PLHFak/Vitrine_lenticulaire/docs/thumbs/base_cplt.jpg

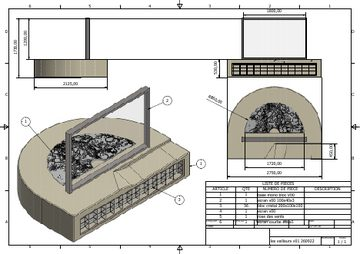
docs/thumbs/base_cplt.jpg
