PLHFak/Vitrine_lenticulaire/docs/ao/LV-AQ-CONS-02_consultation_aquarium_v02-4_NL.pdf

PROJECT
LES VEILLEURS — Beaufort 27

KUNSTENAAR · ONTWERPER
Eva L'Hoest · +32 495 57 92 12 · eva.lhoest@gmail.com

ELEKTROMECHANISCH ASSISTENT
Gioacchino Miceli · +32 497 84 45 10 gioacchino.miceli@thefaktory.com

DOCUMENT
Kristalvitrine — consultatie

ONDERWERP
Rvs kast, glazen deksel, dichting

DOCUMENTNR.
LV-AQ-CONS-02

REVISIE
v02.3

DATUM · UUR
25-09-2026 · 03:10

STATUS
CONSULTATIE

PAGINA
1 / 9

© Eva L'Hoest 2026 — Vertrouwelijk. Reproductie, verspreiding of gebruik buiten deze consultatie verboden zonder schriftelijke toestemming van de kunstenaar. Maten niet contractueel.

# Les Veilleurs — Kristalvitrine (“aquarium”)

Consultatiedossier v02.3 · september 2026 · roestvrijstaalbouw / metaalschrijnwerk — vraag om constructief advies en prijsraming

## 1. Waar gaat het om

Een permanent kunstwerk aan de Belgische kust (Beaufort 27, Noordzee). In de stenen sokkel toont een nis 33 lasergegraveerde optische kristalblokken op een zwarte achtergrond achter een glasplaat, in een droge stikstofatmosfeer die ze beschermt tegen zeevocht. We zoeken een werkplaats om deze nis te bouwen: een gelaste, luchtdichte roestvrijstalen kast en haar afneembaar beglaasd deksel. Het is een uniek, ambachtelijk stuk, gemaakt om minstens tien jaar buiten mee te gaan en ter plaatse geopend en onderhouden te worden. De maten hieronder zijn ons voorstel; uw mening over wat eenvoudiger, veiliger of goedkoper te maken is, interesseert ons evenzeer als uw prijs.

## 2. Hoofdmaten

Element | Maat / waarde | Opmerking
Nuttige binnenholte L × H × D | 2 204 × 333 × ~106 mm | 11 blokken van 200 per rij + 4 mm vulplaatjes; 3 rijen van 100 + 3 mm bovenspeling + 30 mm reserve; diepte: zwarte achtergrond 4 + samengedrukt schuim 8 + blok 100 − de blokken raken het glas, 6 mm vóór het kadervlak
Kast buitenmaat (plaat) | 2 324 × 453 × ~138 mm | = vlak kader van 60 mm rond de holte; 138 = plaat → voorvlak van de lijst = steenvlak
Nis in de stenen sokkel | sponning ≈ 64 × 32 rondom | de kast zit ingebed in de steen; de sponning ontvangt kader + lijst (4 mm speling), het steenvlak ligt gelijk met het glas
Zichtbaar kader vooraan | 60 mm | de kunstenaar wil het zo discreet mogelijk: 50 mm welkom als de sponning het toelaat
Gelaagd extra-helder glas 66.2, antireflex | ≈ 2 264 × 393 × 13 mm — ≈ 29 kg | 2 × 6 mm ijzerarm + PVB; antireflexlaag op de buitenzijde; gepolijste randen
K9-kristalblokken | 33 × (200 × 100 × 100) — ≈ 166 kg | door ons geleverd en geplaatst, ter plaatse
Massa geladen | ≈ 350 kg | kast ≈ 60, kader ≈ 26, klemlijsten ≈ 63, glas ≈ 29, blokken ≈ 166
Klemschroeven | ≈ 110 × M4×30 verzonken Torx, steek 50 | geen enkele schroef gaat door het glas
Dichting | EPDM-koord Ø10, ~30 % samengedrukt in een groef van 2 mm | de aanslag van de lijst bepaalt de samendrukking, niet het aanhaalmoment


PROJECT
LES VEILLEURS — Beaufort 27

DOCUMENT
Kristalvitrine — consultatie

STATUS
CONSULTATIE

PAGINA
2 / 9

PROJECT


LES VEILLEURS — Beaufort 27

DOCUMENT
Kristalvitrine — consultatie

STATUS
CONSULTATIE

PAGINA
3 / 9

## 3. Beschrijving stuk per stuk

3.1 Kast (rvs 316L, plaat 3 mm) — Plaat in U geplooid (achterwand + boven- en onderwand), binnenradius ≤ 3 mm. Twee eindflenzen 3 mm met doorlopende lasnaad, binnennaden vlak geslepen: de holte moet glad blijven, de blokken schuiven tegen de wanden. Verstijvers uitsluitend aan de buitenzijde: 3 horizontale en 4 verticale hoekprofielen 40×40×4, puntgelast (30/150). De achterwand mag niet meer dan 1 mm doorbuigen onder 170 kg verdeelde blokken. Twee buisaansluitingen Ø10 × 1 gelast in de bovenste achterwand, aan beide uiteinden, 200 mm recht, gladde uiteinden (knelkoppeling). Twee afneembare hijsogen M8 bovenaan.
3.2 Voorkader (rvs platstaal 60×10) — Rondom de opening gelast, verstek- of overlappende hoeken, daarna voorvlak na het lassen vlak bewerkt: vlakheid ≤ 0,3 mm/m (dit is het draagvlak van de dichting). Getapte gaten M4, as op 15 mm van de buitenrand, steek 50, twee gaten op 25 mm van elke hoek. Positioneergroef voor het koord: breedte 11, diepte 2, as op 40 mm van de buitenrand (op een derde van de breedte aan de binnenzijde, weg van de glasrand), doorlopend, afgeronde hoeken R10.
3.3 Deksel: vier bewerkte klemlijsten (rvs 316L, 60×24) — Profiel: volle hiel 28×24 die op het kader rust, sponning 32×19 aan de binnenzijde voor het glas (rubberband 1 mm + 13 mm + speling), lip van 5 mm vooraan. Verzonken boringen M4 tegenover de tapgaten. Hoekverbinding voor te stellen door de werkplaats (gedeuvelde en verlijmde verstek, of hoeken uit het volle gefreesd). Zichtbare afwerking: geborsteld of gepolijst, staal af te spreken.

3.4 Glas en plaatsing in de sponning — Gelaagd extra-helder glas 66.2: twee ijzerarme ruiten van 6 mm (type AGC Clearvision, Saint-Gobain Diamant, Pilkington Optiwhite) met twee heldere PVB-folies, dus 13 mm. Antireflexlaag op de buitenzijde (zijde 1) — duurzame magnetroncoating type AGC Clearsight, Pilkington OptiView of Glas Trösch Luxar Classic — zodat de gravures leesbaar blijven onder de Noordzeehemel; geen coating op de binnenzijde, waar de blokken rechtstreeks aanliggen. Gepolijste randen. Geen verlijming: het glas rust in de sponning op een zelfklevende rubberband van ongeveer 1 mm dik en 30 mm breed, gekleefd op de sponningbodem van de lijst; geen glas-metaalcontact, het glas blijft demonteerbaar. Het glas kan van uw gebruikelijke glazenmaker of van de onze komen: geef dit aan in uw antwoord.
3.5 Dichting en schroeven — Vol EPDM-koord Ø10, gevulkaniseerd tot een doorlopend kader op de groefmaten (+ 1 reserve). Schroeven M4×30 verzonken Torx T20 rvs A4, kruiselings aangehaald, ongeveer 2 N·m; de hiel van de lijst komt tegen het kader op 5 mm boven de groefbodem: de samendrukking van de dichting is overal gelijk, ongeacht de ijver van wie schroeft.
3.6 Optie: ledstrip bovenin de kast — Een waterdicht ledprofiel (IP67, 24 V, ~3 W, 3000 K, lengte ≈ 2 100 mm) onder de bovenwand, binnen in de holte, voor neerwaarts strijklicht op de blokken. Wij leveren het profiel; wij vragen u de bevestiging te begroten (twee rails of lippen gelast onder de bovenwand, 3 mm reserve) en een derde dichte aansluiting Ø6 in de bovenste achterwand voor de kabel, met rvs wartel.
3.7 Nis in de steen — De kast zit rondom ingebed in de monolithische stenen sokkel (onder, boven, achter, zijkanten). Vóór het kader is de steen uitgespaard met een sponning van ongeveer 64 mm breed en 32 mm diep die kader en lijst met 4 mm speling opneemt, zodat het steenvlak gelijk ligt met het lijstvlak en het glas. Deze sponning wordt door de steenhouwerij gekapt op basis van uw definitieve maten.

## 4. Tekeningen

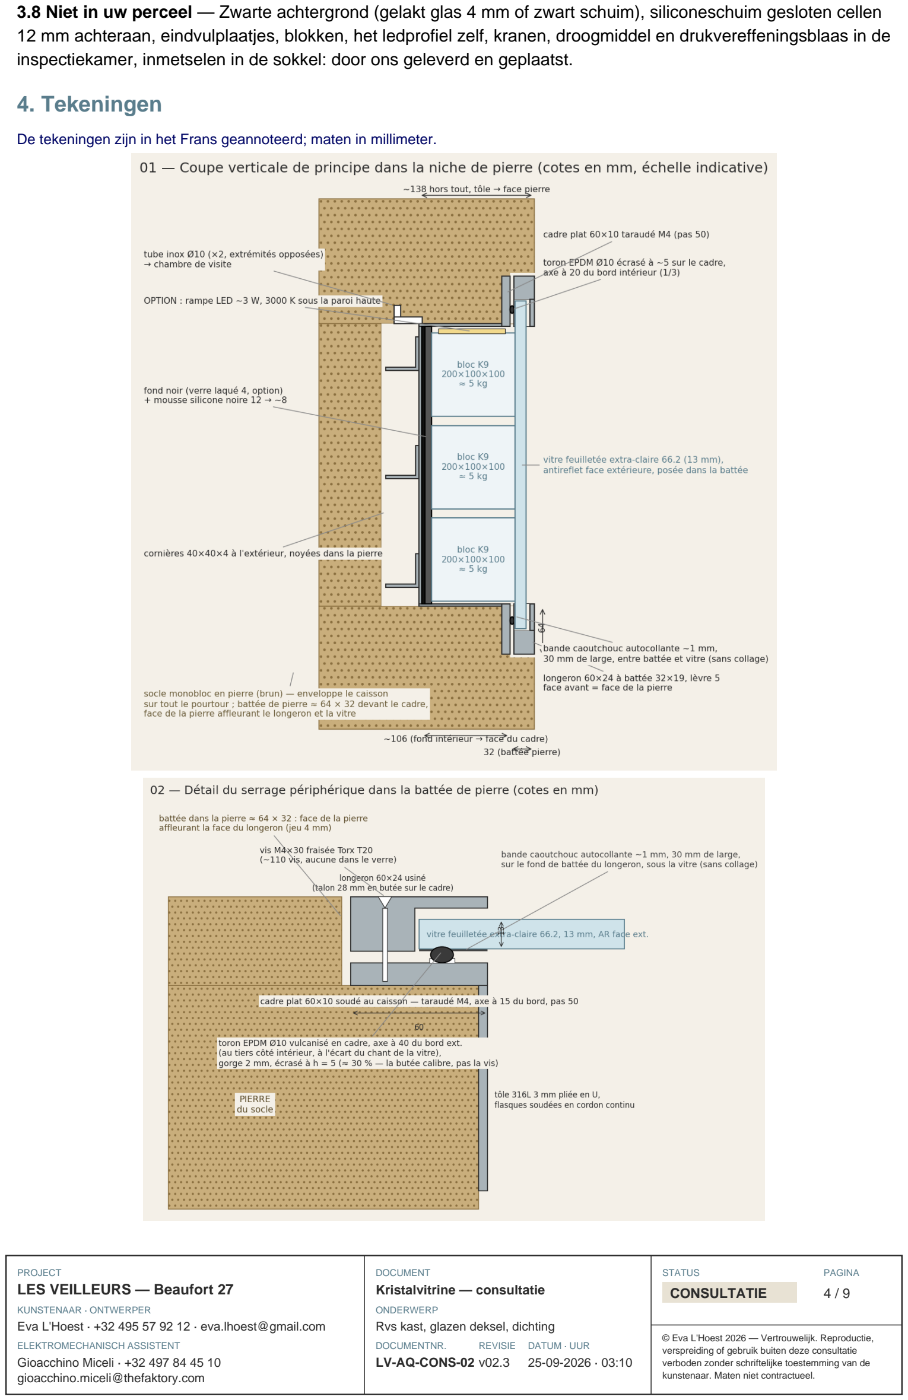
[picture p34: page 4]

PROJECT
LES VEILLEURS — Beaufort 27

DOCUMENT
Kristalvitrine — consultatie

STATUS
CONSULTATIE

PAGINA
4 / 9

3.8 Niet in uw perceel — Zwarte achtergrond (gelakt glas 4 mm of zwart schuim), siliconeschuim gesloten cellen 12 mm achteraan, eindvulplaatjes, blokken, het ledprofiel zelf, kranen, droogmiddel en drukvereffeningsblaas in de inspectiekamer, inmetselen in de sokkel: door ons geleverd en geplaatst.

De tekeningen zijn in het Frans geannoteerd; maten in millimeter.

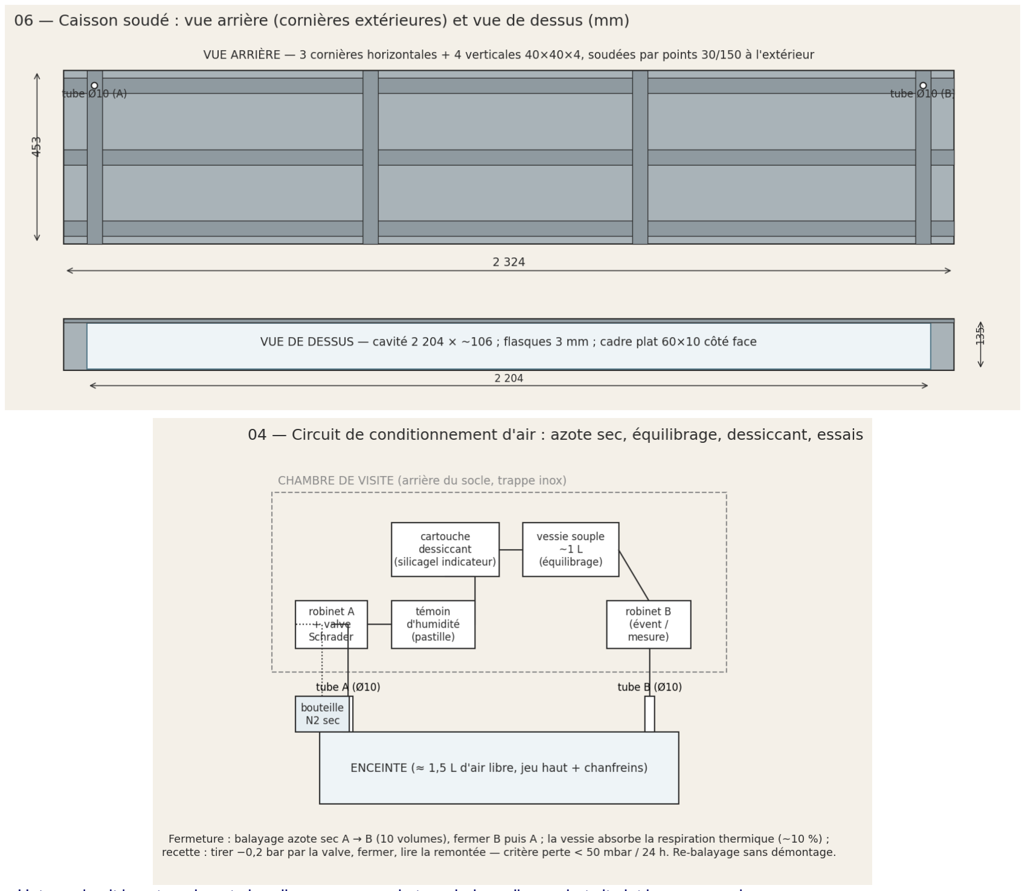
[picture p35: figure]

PROJECT
LES VEILLEURS — Beaufort 27

DOCUMENT
Kristalvitrine — consultatie

STATUS
CONSULTATIE

PAGINA
5 / 9

Het gascircuit is getoond om te begrijpen waarvoor de twee buizen dienen; het zit niet in uw perceel.

## 4 bis. Geëxplodeerde 3D-aanzichten

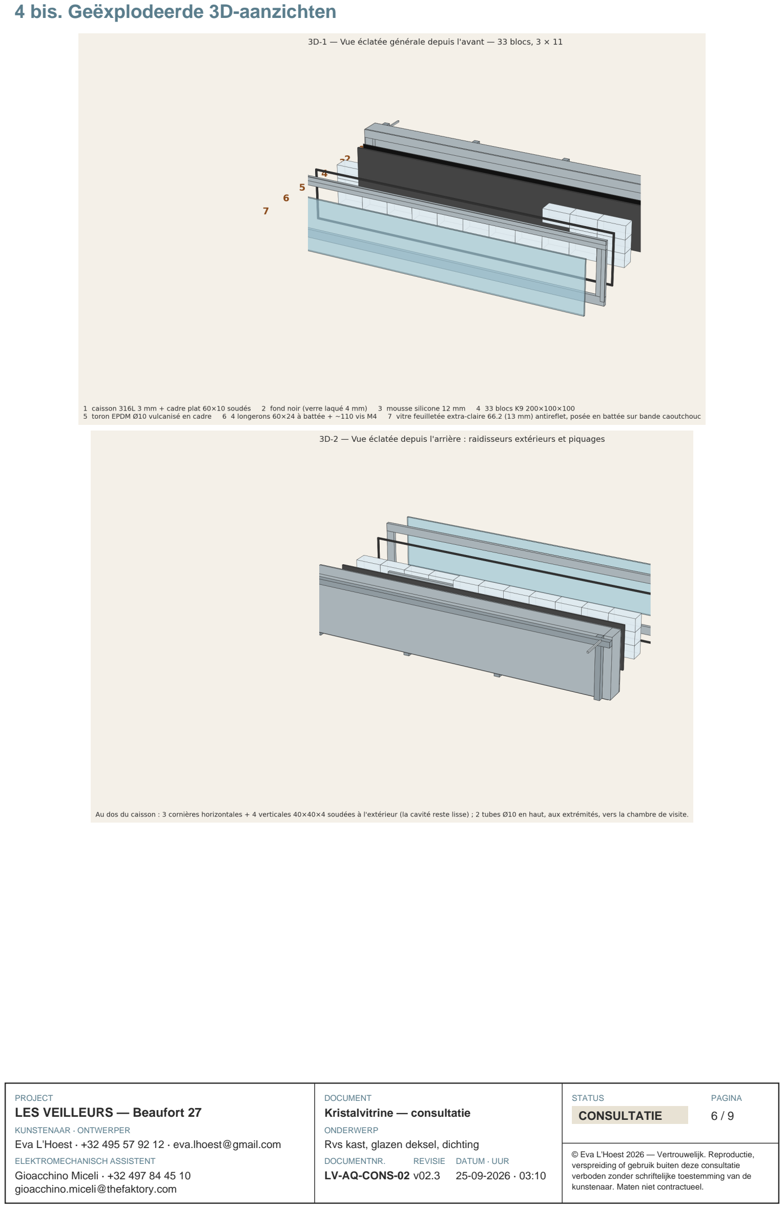
[picture p36: page 6]

PROJECT
LES VEILLEURS — Beaufort 27

DOCUMENT
Kristalvitrine — consultatie

STATUS
CONSULTATIE

PAGINA
6 / 9

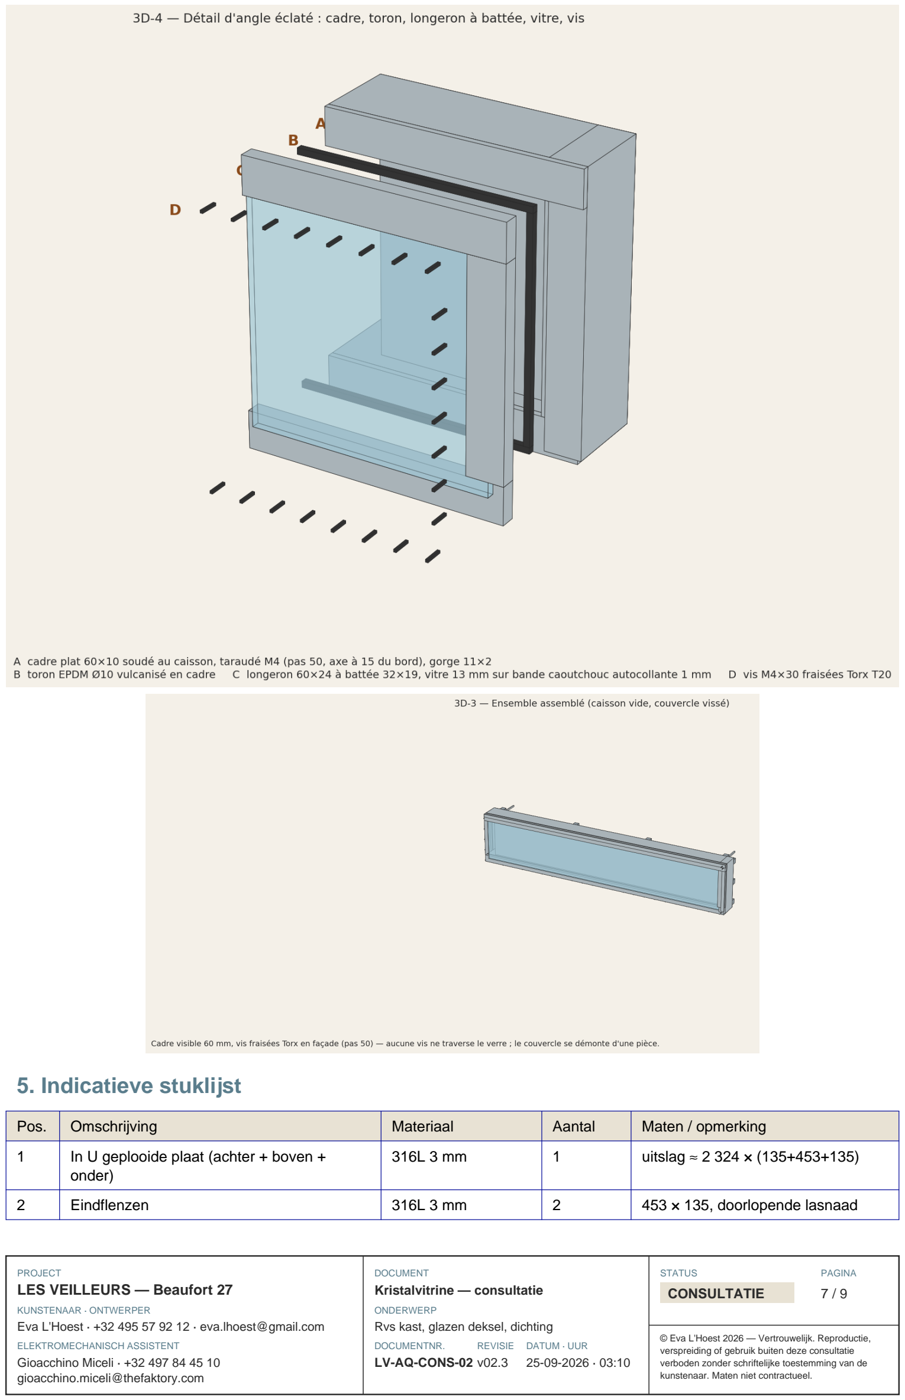
[picture p37: page 7]

PROJECT
LES VEILLEURS — Beaufort 27

DOCUMENT
Kristalvitrine — consultatie

STATUS
CONSULTATIE

PAGINA
7 / 9

## 5. Indicatieve stuklijst

Pos. | Omschrijving | Materiaal | Aantal | Maten / opmerking
1 | In U geplooide plaat (achter + boven + onder) | 316L 3 mm | 1 | uitslag ≈ 2 324 × (135+453+135)
2 | Eindflenzen | 316L 3 mm | 2 | 453 × 135, doorlopende lasnaad

PROJECT
LES VEILLEURS — Beaufort 27

DOCUMENT
Kristalvitrine — consultatie

STATUS
CONSULTATIE

PAGINA
8 / 9
Pos. | Omschrijving | Materiaal | Aantal | Maten / opmerking
3 | Uitwendige verstijvingshoeken | 316L 40×40×4 | 7 | 3 × 2 324 + 4 × 453
4 | Vlak voorkader | 316L 60×10 | ≈ 5,6 m | getapt M4 steek 50, groef 11×2, vlak bewerkt
5 | Klemlijsten met sponning | 316L 60×24 bewerkt | 4 | 2 × 2 324 + 2 × 453 (hoeken te bepalen)
6 | Gelaagd extra-helder antireflexglas | 66.2 ijzerarm, AR zijde 1 | 1 | ≈ 2 264 × 393, gepolijste randen
7 | Zelfklevende rubberband (EPDM of silicone) 30 × 1 mm | rubber | ≈ 6 m | op de sponningbodem van de lijst
8 | EPDM-koord Ø10 gevulkaniseerd kader | EPDM 70 Sh | 1 + 1 | omtrek ≈ 5,5 m
9 | Schroeven M4×30 verzonken Torx T20 | rvs A4 | ≈ 115 | kruiselings aanhalen
10 | Buisaansluitingen Ø10×1 | 316L | 2 | 200 mm, gladde uiteinden
11 | Afneembare hijsogen | rvs M8 | 2 | bovenaan
12 | Led-optie: aansluiting Ø6 + wartel + bevestiging profiel | 316L | 1 | ledprofiel door ons geleverd

## 6. Wat wij u vragen

Perceel | Inhoud | Te begroten
A — Kast | pos. 1 t/m 4, 10, 11: plooien, dicht lassen, verstijvers, vlak kader, tappen, groef | vaste prijs + levertermijn
B — Deksel | pos. 5: 4 bewerkte lijsten, hoekverbinding, boringen, afwerking | vaste prijs + levertermijn
C — Beglazing | pos. 6 en 7: gelaagd extra-helder antireflexglas en rubberband (glas door u of uw glazenmaker) | prijs, of “buiten perceel” als u liever hebt dat wij het leveren
D — Dichting en schroeven | pos. 8 en 9 | prijs
E — Droge test | deksel vastgeschroefd zonder blokken, −0,2 bar via de buizen, 24 u houden (verlies < 50 mbar) | prijs, of inbegrepen
Optie 1 | zichtbaar kader beperkt tot 50 mm (plat 50×10 + lijst 50×24, sponning 24) | meer-/minprijs, haalbaarheid
Optie 2 | zichtbare afwerking van de lijsten: geborsteld / spiegelglans | meerprijs
Optie 3 | ledstrip bovenin de kast: bevestiging onder de bovenwand + dichte aansluiting Ø6 (pos. 12) | meerprijs
Levering | lege kast en gedemonteerd deksel, beschermd, naar een steenhouwerij (België of Zwitserland, nader te bepalen) | transportprijs of af werkplaats

## 7. Uw mening interesseert ons over

- Geplooide plaat 3 mm + uitwendige hoeken: voldoende voor de vlakheid van de achterwand, of verkiest u 4 mm?
- Vlak bewerken van het kader na het lassen: frezen, of volstaat handmatig richten voor ≤ 0,3 mm/m?
- Hoekverbinding van de lijsten: verstek, hoeken uit het volle, of gelast kader in één stuk bewerkt?
- Vol koord (30 %) of hol buiskoord (50 %): wat houdt buiten het langst stand?
- Standaard of onbreekbare (TR) Torx voor de schroeven vooraan?
- Alles wat volgens u de fabricage vereenvoudigt zonder het uitzicht te veranderen: discreet kader, geen schroef in het glas, demonteerbaar.

## 8. Planning en vervolg

PROJECT
LES VEILLEURS — Beaufort 27

DOCUMENT
Kristalvitrine — consultatie

STATUS
CONSULTATIE

PAGINA
9 / 9
Stap | Termijn
Uw constructief advies en prijsraming | binnen 3 weken
Goedkeuring door de kunstenaar, daarna gemaatvoerde uitvoeringstekeningen (PDF + STEP/DXF) | 2 tot 3 weken
Vaste prijs en bestelling | bij ontvangst van de tekeningen
Fabricage en droge test in de werkplaats | 4 tot 6 weken na bestelling
Levering aan de sokkel (hoofdwerkplaats) | samen af te spreken, winter 2026-2027
Een staal van 200 mm klemlijst met koord, rubberband en een stuk glas zou een goede eerste stap zijn: laat ons weten of u dit kunt maken en tegen welke prijs.
