PLHFak/Vitrine_lenticulaire/docs/ao/LV-AQ-PLANS-01_plans_aquarium_EN.pdf

Les Veilleurs — Crystal 'aquarium' showcase — Drawings (LV-AQ-PLANS-01, rev. 1, 29-09-2026)

# Set of drawings for the stainless box lot · drawings labelled in French

1. LV-AQ-PL-01 | Principle vertical section
2. LV-AQ-PL-02 | Detail of the peripheral clamping
3. LV-AQ-PL-03 | Dimensioned front view and plan (3 × 11 blocks)
4. LV-AQ-PL-04 | Gas circuit: dry nitrogen, bladder, desiccant
5. LV-AQ-PL-05 | Assembly sequence
6. LV-AQ-PL-06 | Welded box: rear and top views
7. LV-AQ-PL-07 | Profile of the 60×24 rebated bar
8. LV-AQ-3D-01 | Exploded view from the front
9. LV-AQ-3D-02 | Exploded view from the rear
10. LV-AQ-3D-03 | Assembled unit
11. LV-AQ-3D-04 | Exploded corner detail

Key French terms: caisson = box · cadre = frame · longeron = clamping bar · battée = rebate · vitre = glass pane · toron / joint = gasket cord · vis = screw · piquage = pipe stub · socle = base. Drawings prepared with the help of AI under the team's control — subject to the workshop's shop drawings. Dimensions not contractual.

© Eva L'Hoest 2026 — Confidentiel / Confidential. Cotes non contractuelles / Dimensions not contractual.

# Les Veilleurs — Vitrine « aquarium » des cristaux — Coupe verticale de principe

## LV-AQ-PL-01 · rév. 3 · 25-09-26 · CONSULTATION · schéma légendé en français

PROJET

## LES VEILLEURS — Beaufort 27

ARTISTE · MAÎTRE D'ŒUVRE

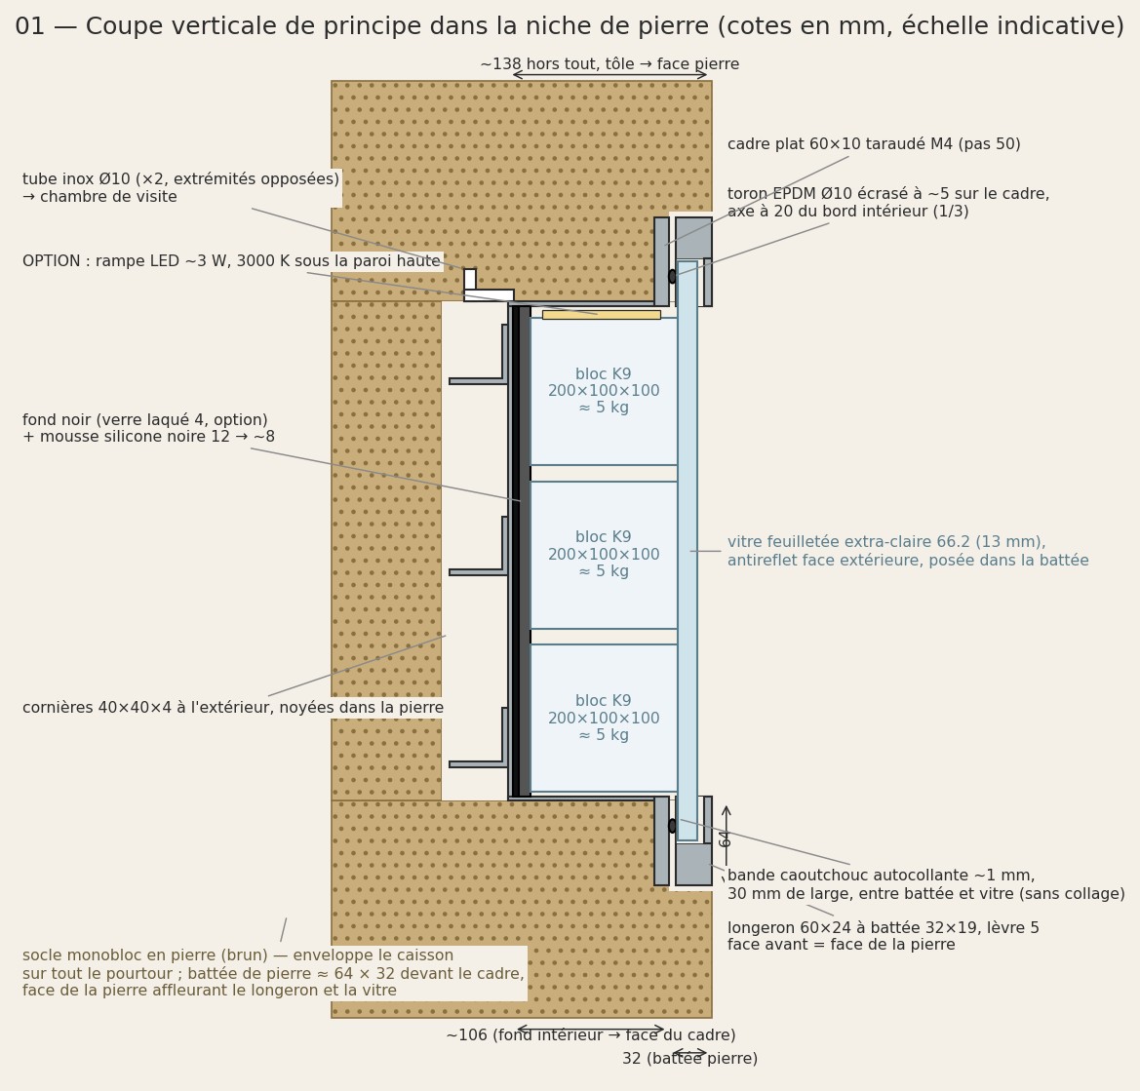
[picture p39: figure]

## Eva L'Hoest · +32 495 57 92 12 · eva.lhoest@gmail.com

ASSISTANT ÉLECTROMÉCANIQUE

## Gioacchino Miceli · +32 497 84 45 10 · gioacchino.miceli@thefaktory.com

DOCUMENT

## Vitrine « aquarium » des cristaux — Coupe verticale de principe

OBJET

## Caisson inox, couvercle vitré, joint et azote sec

N° DOCUMENT · RÉVISION · DATE · HEURE

## LV-AQ-PL-01 · rév. 3 · 25-09-26

EN LIGNE

### https://aquarium-k9.vercel.app

STATUT

## CONSULTATION

© Eva L'Hoest 2026 — Confidentiel. Reproduction, diffusion ou usage hors de cette consultation interdits sans accord écrit de l'artiste. Cotes non contractuelles.

# Les Veilleurs — Vitrine « aquarium » des cristaux — Détail du serrage périphérique

## LV-AQ-PL-02 · rév. 3 · 25-09-26 · CONSULTATION · schéma légendé en français

PROJET

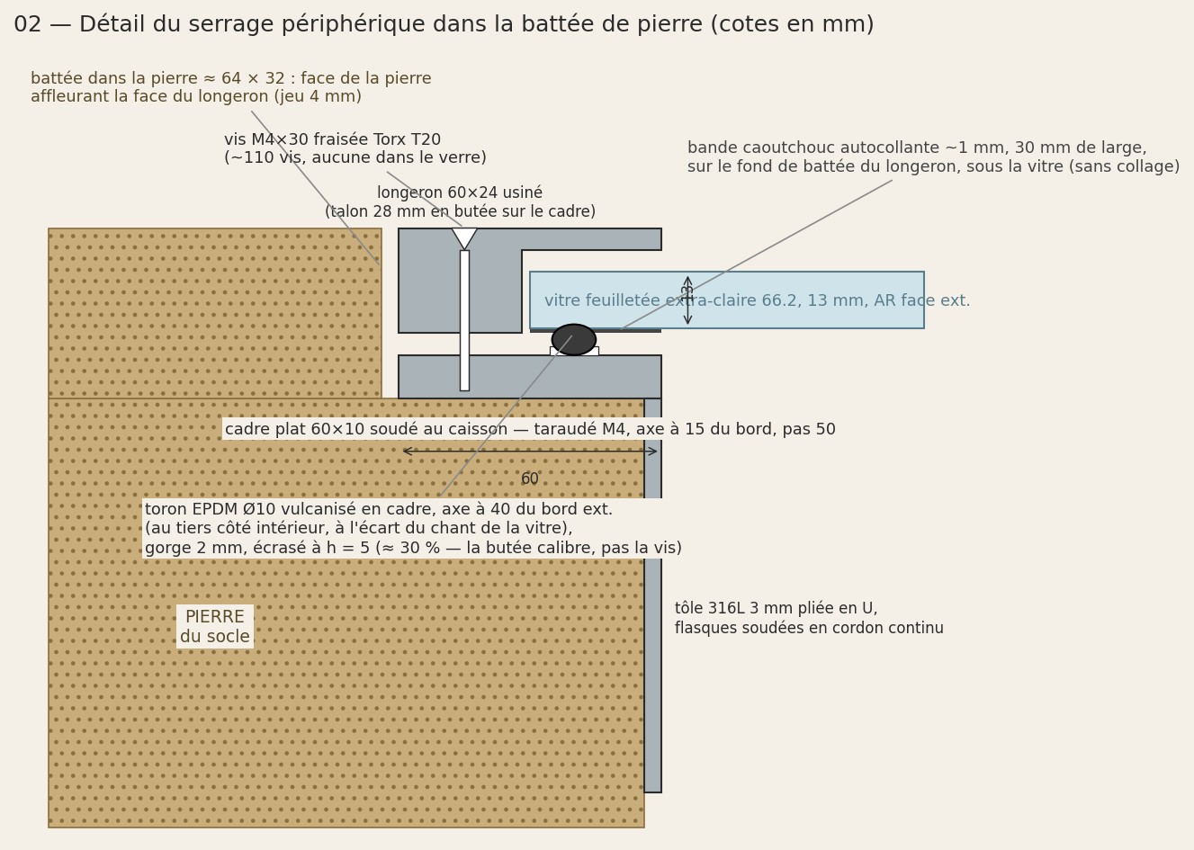
[picture p40: figure]

## LES VEILLEURS — Beaufort 27

ARTISTE · MAÎTRE D'ŒUVRE

## Eva L'Hoest · +32 495 57 92 12 · eva.lhoest@gmail.com

ASSISTANT ÉLECTROMÉCANIQUE

## Gioacchino Miceli · +32 497 84 45 10 · gioacchino.miceli@thefaktory.com

DOCUMENT

## Vitrine « aquarium » des cristaux — Détail du serrage périphérique

OBJET

## Caisson inox, couvercle vitré, joint et azote sec

N° DOCUMENT · RÉVISION · DATE · HEURE

## LV-AQ-PL-02 · rév. 3 · 25-09-26

STATUT

## CONSULTATION

© Eva L'Hoest 2026 — Confidentiel. Reproduction, diffusion ou usage hors de cette consultation interdits sans accord écrit de l'artiste. Cotes non contractuelles.

Les Veilleurs — Vitrine « aquarium » des cristaux — Vue de face et plan cotés (3 × 11 blocs)

## LV-AQ-PL-03 · rév. 2 · 25-09-26 · CONSULTATION · schéma légendé en français

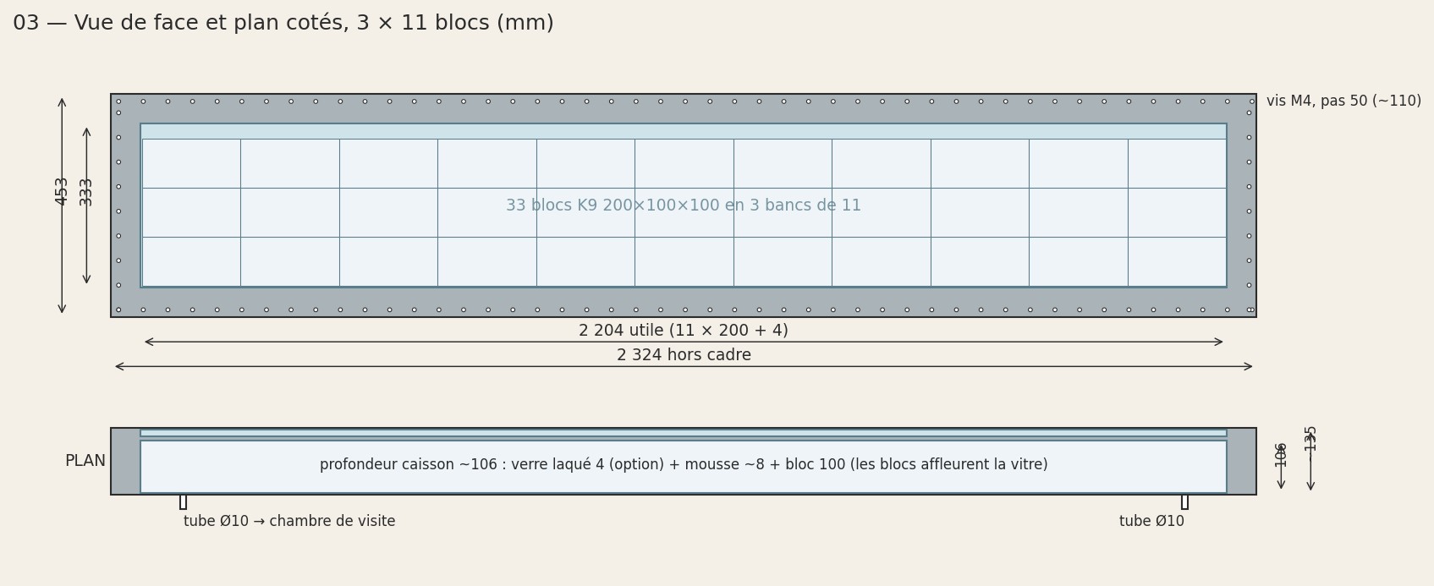
[picture p41: figure]

PROJET

## LES VEILLEURS — Beaufort 27

ARTISTE · MAÎTRE D'ŒUVRE

## Eva L'Hoest · +32 495 57 92 12 · eva.lhoest@gmail.com

ASSISTANT ÉLECTROMÉCANIQUE

## Gioacchino Miceli · +32 497 84 45 10 · gioacchino.miceli@thefaktory.com

DOCUMENT

## Vitrine « aquarium » des cristaux — Vue de face et plan cotés (3 × 11 blocs)

OBJET

## Caisson inox, couvercle vitré, joint et azote sec

N° DOCUMENT · RÉVISION · DATE · HEURE

## LV-AQ-PL-03 · rév. 2 · 25-09-26

STATUT

## CONSULTATION

© Eva L'Hoest 2026 — Confidentiel. Reproduction, diffusion ou usage hors de cette consultation interdits sans accord écrit de l'artiste. Cotes non contractuelles.

Les Veilleurs — Vitrine « aquarium » des cristaux — Circuit gaz : azote sec, vessie, dessiccant

## LV-AQ-PL-04 · rév. 1 · 25-09-26 · CONSULTATION · schéma légendé en français

PROJET

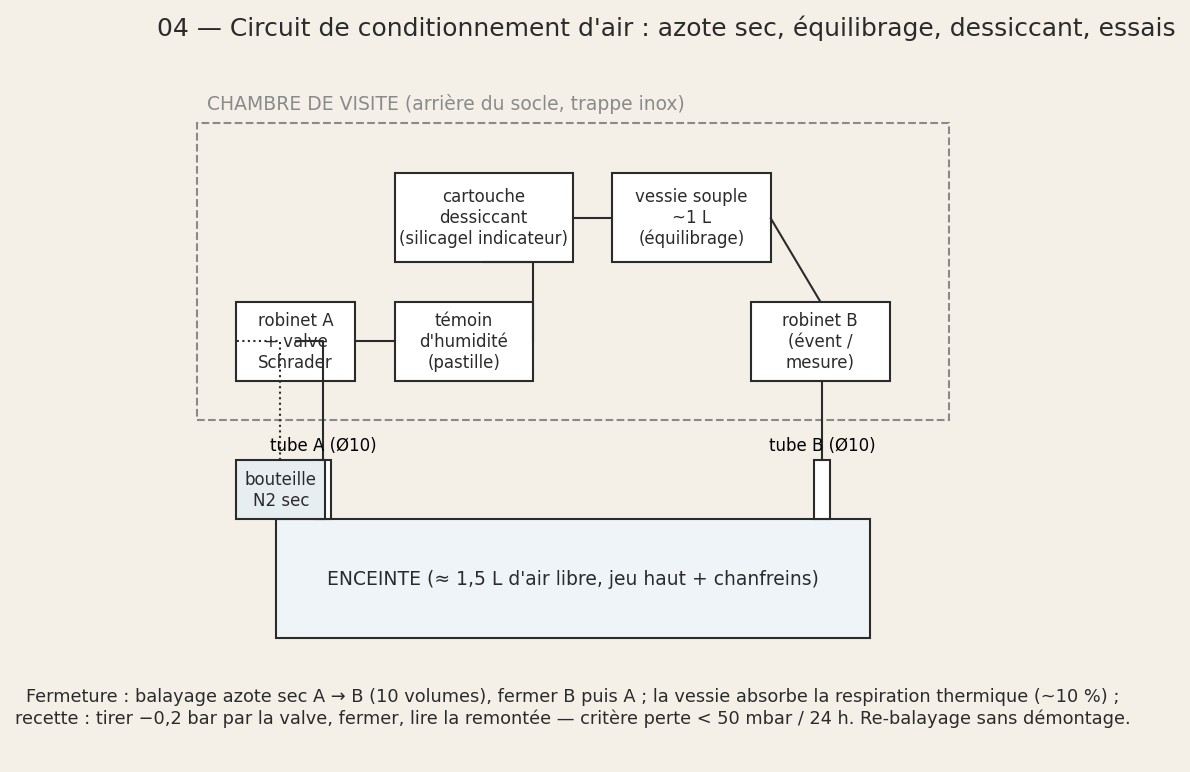
[picture p42: figure]

## LES VEILLEURS — Beaufort 27

ARTISTE · MAÎTRE D'ŒUVRE

## Eva L'Hoest · +32 495 57 92 12 · eva.lhoest@gmail.com

ASSISTANT ÉLECTROMÉCANIQUE

## Gioacchino Miceli · +32 497 84 45 10 · gioacchino.miceli@thefaktory.com

DOCUMENT

## Vitrine « aquarium » des cristaux — Circuit gaz : azote sec, vessie, dessiccant

OBJET

## Caisson inox, couvercle vitré, joint et azote sec

N° DOCUMENT · RÉVISION · DATE · HEURE

## LV-AQ-PL-04 · rév. 1 · 25-09-26

STATUT

## CONSULTATION

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

# Les Veilleurs — Vitrine « aquarium » des cristaux — Séquence de montage

## LV-AQ-PL-05 · rév. 1 · 25-09-26 · CONSULTATION · schéma légendé en français

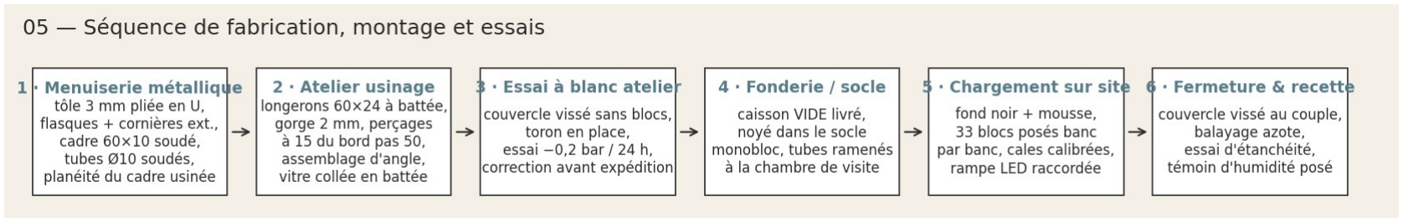
[picture p43: figure]

PROJET

## LES VEILLEURS — Beaufort 27

ARTISTE · MAÎTRE D'ŒUVRE

## Eva L'Hoest · +32 495 57 92 12 · eva.lhoest@gmail.com

ASSISTANT ÉLECTROMÉCANIQUE

## Gioacchino Miceli · +32 497 84 45 10 · gioacchino.miceli@thefaktory.com

DOCUMENT

## Vitrine « aquarium » des cristaux — Séquence de montage

OBJET

## Caisson inox, couvercle vitré, joint et azote sec

N° DOCUMENT · RÉVISION · DATE · HEURE

## LV-AQ-PL-05 · rév. 1 · 25-09-26

STATUT

## CONSULTATION

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

Les Veilleurs — Vitrine « aquarium » des cristaux — Caisson soudé : vue arrière et vue de dessus

## LV-AQ-PL-06 · rév. 1 · 25-09-26 · CONSULTATION · schéma légendé en français

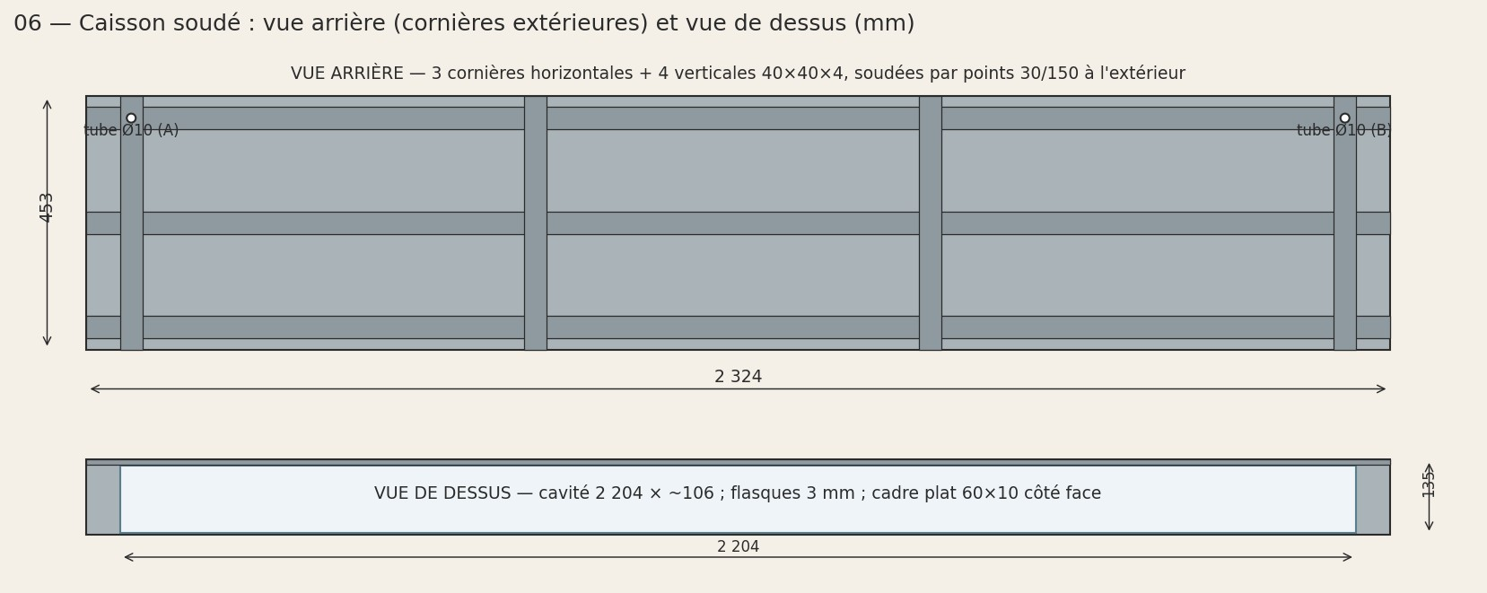
[picture p44: figure]

PROJET

## LES VEILLEURS — Beaufort 27

ARTISTE · MAÎTRE D'ŒUVRE

## Eva L'Hoest · +32 495 57 92 12 · eva.lhoest@gmail.com

ASSISTANT ÉLECTROMÉCANIQUE

## Gioacchino Miceli · +32 497 84 45 10 · gioacchino.miceli@thefaktory.com

DOCUMENT

## Vitrine « aquarium » des cristaux — Caisson soudé : vue arrière et vue de dessus

OBJET

## Caisson inox, couvercle vitré, joint et azote sec

N° DOCUMENT · RÉVISION · DATE · HEURE

## LV-AQ-PL-06 · rév. 1 · 25-09-26

STATUT

## CONSULTATION

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

# Les Veilleurs — Vitrine « aquarium » des cristaux — Profil du longeron à battée 60×24

## LV-AQ-PL-07 · rév. 2 · 25-09-26 · CONSULTATION · schéma légendé en français

PROJET

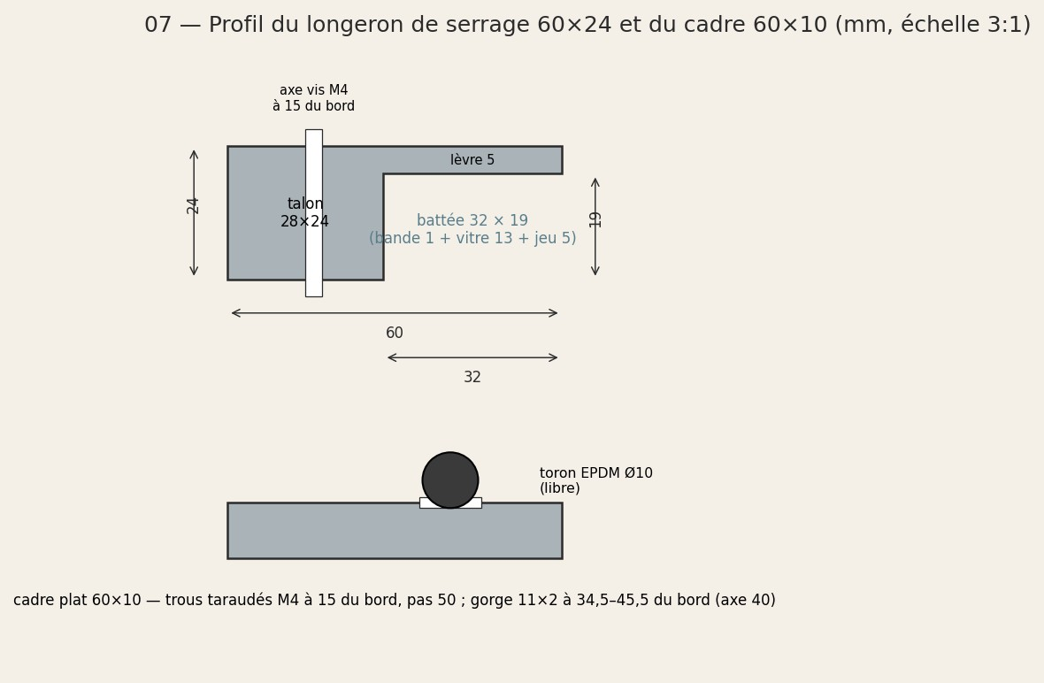
[picture p45: figure]

## LES VEILLEURS — Beaufort 27

ARTISTE · MAÎTRE D'ŒUVRE

## Eva L'Hoest · +32 495 57 92 12 · eva.lhoest@gmail.com

ASSISTANT ÉLECTROMÉCANIQUE

## Gioacchino Miceli · +32 497 84 45 10 · gioacchino.miceli@thefaktory.com

DOCUMENT

## Vitrine « aquarium » des cristaux — Profil du longeron à battée 60×24

OBJET

## Caisson inox, couvercle vitré, joint et azote sec

N° DOCUMENT · RÉVISION · DATE · HEURE

## LV-AQ-PL-07 · rév. 2 · 25-09-26

STATUT

## CONSULTATION

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

# Les Veilleurs — Vitrine « aquarium » des cristaux — Vue éclatée depuis l'avant

## LV-AQ-3D-01 · rév. 1 · 25-09-26 · CONSULTATION · schéma légendé en français

PROJET

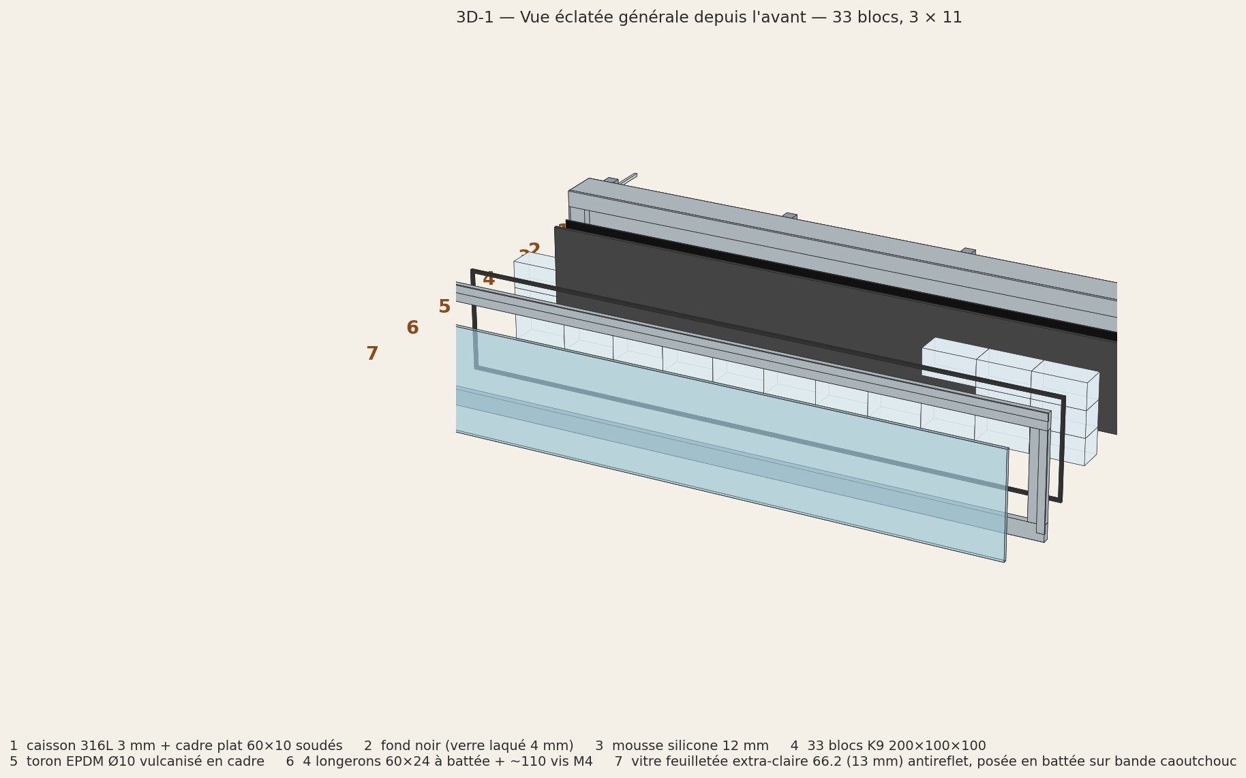
[picture p46: figure]

## LES VEILLEURS — Beaufort 27

ARTISTE · MAÎTRE D'ŒUVRE

## Eva L'Hoest · +32 495 57 92 12 · eva.lhoest@gmail.com

ASSISTANT ÉLECTROMÉCANIQUE

## Gioacchino Miceli · +32 497 84 45 10 · gioacchino.miceli@thefaktory.com

DOCUMENT

## Vitrine « aquarium » des cristaux — Vue éclatée depuis l'avant

OBJET

## Caisson inox, couvercle vitré, joint et azote sec

N° DOCUMENT · RÉVISION · DATE · HEURE

## LV-AQ-3D-01 · rév. 1 · 25-09-26

STATUT

## CONSULTATION

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

# Les Veilleurs — Vitrine « aquarium » des cristaux — Vue éclatée depuis l'arrière

## LV-AQ-3D-02 · rév. 1 · 25-09-26 · CONSULTATION · schéma légendé en français

PROJET

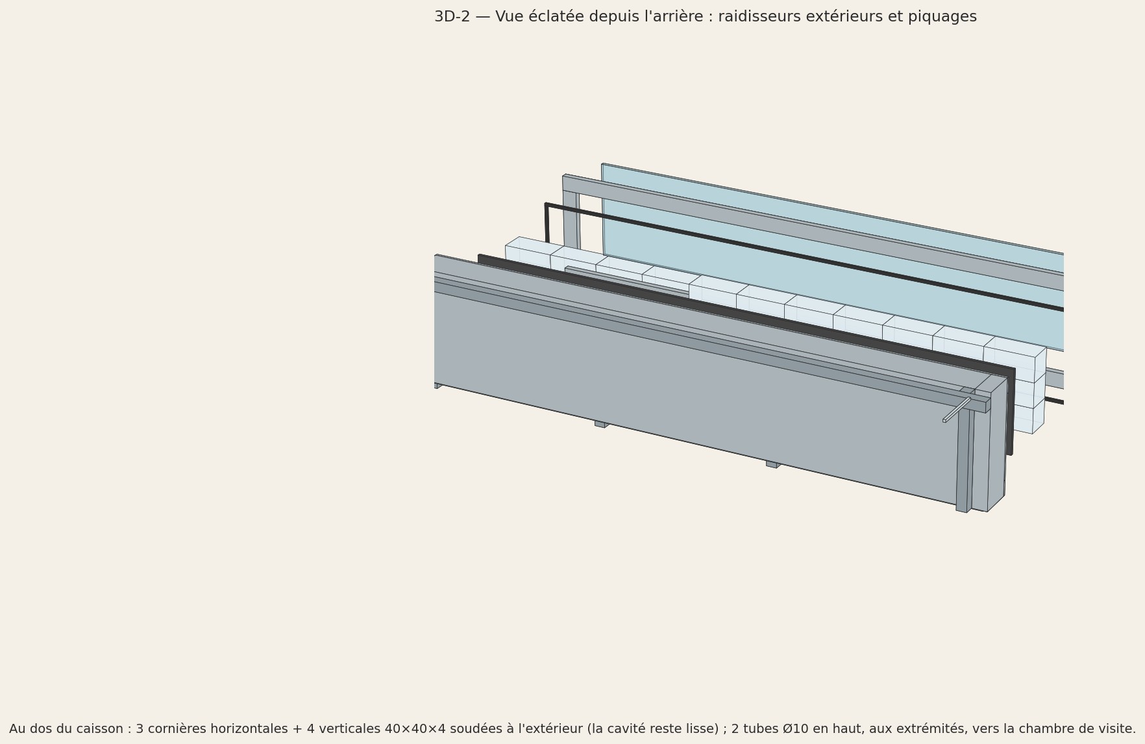
[picture p47: figure]

## LES VEILLEURS — Beaufort 27

ARTISTE · MAÎTRE D'ŒUVRE

## Eva L'Hoest · +32 495 57 92 12 · eva.lhoest@gmail.com

ASSISTANT ÉLECTROMÉCANIQUE

## Gioacchino Miceli · +32 497 84 45 10 · gioacchino.miceli@thefaktory.com

DOCUMENT

## Vitrine « aquarium » des cristaux — Vue éclatée depuis l'arrière

OBJET

## Caisson inox, couvercle vitré, joint et azote sec

N° DOCUMENT · RÉVISION · DATE · HEURE

## LV-AQ-3D-02 · rév. 1 · 25-09-26

STATUT

## CONSULTATION

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

# Les Veilleurs — Vitrine « aquarium » des cristaux — Ensemble assemblé

## LV-AQ-3D-03 · rév. 1 · 25-09-26 · CONSULTATION · schéma légendé en français

PROJET

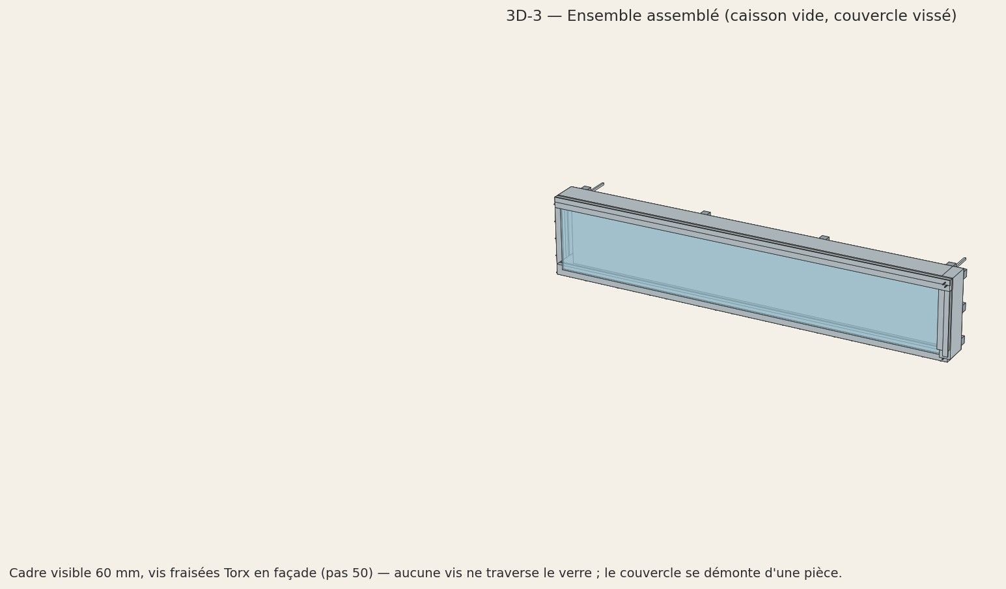
[picture p48: figure]

## LES VEILLEURS — Beaufort 27

ARTISTE · MAÎTRE D'ŒUVRE

## Eva L'Hoest · +32 495 57 92 12 · eva.lhoest@gmail.com

ASSISTANT ÉLECTROMÉCANIQUE

## Gioacchino Miceli · +32 497 84 45 10 · gioacchino.miceli@thefaktory.com

DOCUMENT

## Vitrine « aquarium » des cristaux — Ensemble assemblé

OBJET

## Caisson inox, couvercle vitré, joint et azote sec

N° DOCUMENT · RÉVISION · DATE · HEURE

## LV-AQ-3D-03 · rév. 1 · 25-09-26

STATUT

## CONSULTATION

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

# Les Veilleurs — Vitrine « aquarium » des cristaux — Détail d'angle éclaté

## LV-AQ-3D-04 · rév. 1 · 25-09-26 · CONSULTATION · schéma légendé en français

PROJET

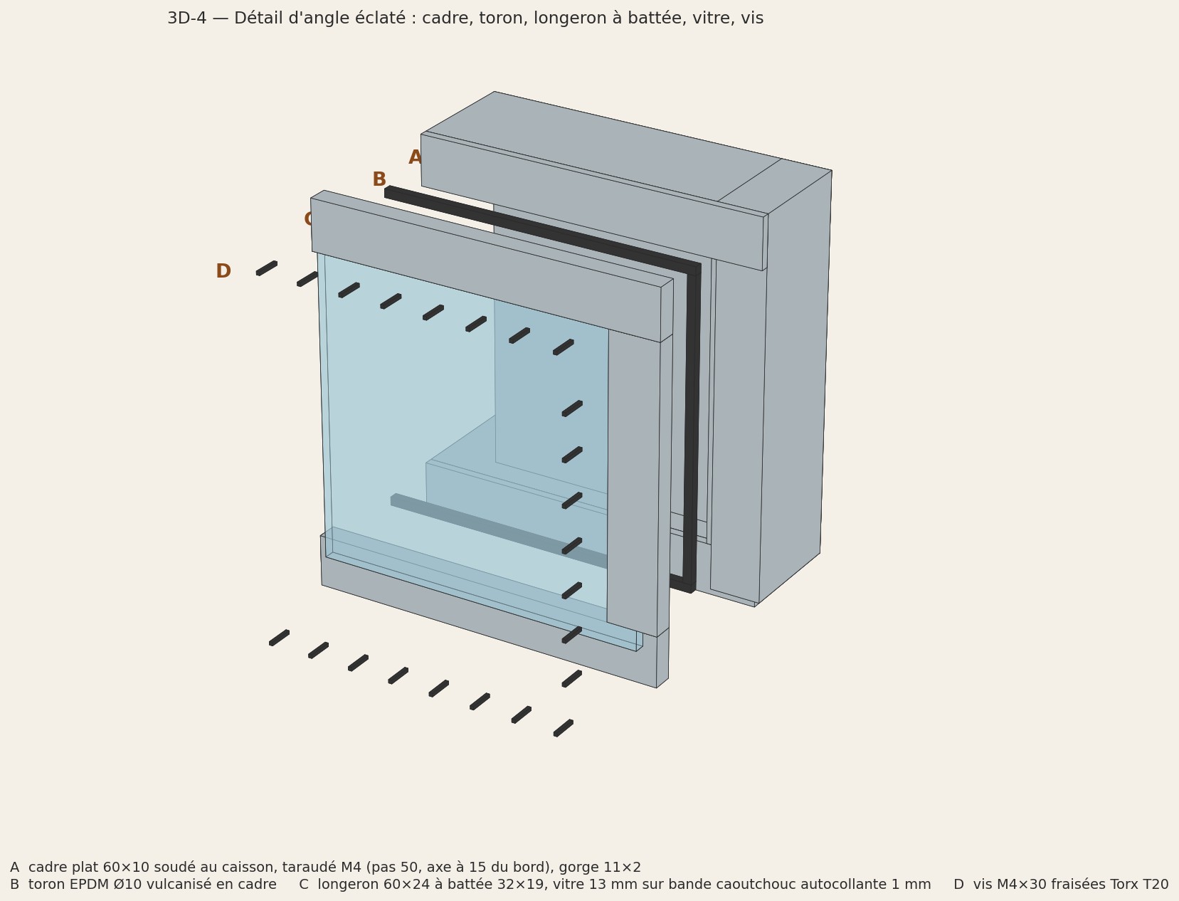
[picture p49: figure]

## LES VEILLEURS — Beaufort 27

ARTISTE · MAÎTRE D'ŒUVRE

## Eva L'Hoest · +32 495 57 92 12 · eva.lhoest@gmail.com

ASSISTANT ÉLECTROMÉCANIQUE

## Gioacchino Miceli · +32 497 84 45 10 · gioacchino.miceli@thefaktory.com

DOCUMENT

## Vitrine « aquarium » des cristaux — Détail d'angle éclaté

OBJET

## Caisson inox, couvercle vitré, joint et azote sec

N° DOCUMENT · RÉVISION · DATE · HEURE

## LV-AQ-3D-04 · rév. 1 · 25-09-26

STATUT

## CONSULTATION

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
