PLHFak/Vitrine_lenticulaire/docs/pdf/LV-VL-CRQ-01_croquis.pdf

Les Veilleurs — La vitrine lenticulaire — Croquis de principe d'origine — coupe dans le montant

## LV-VL-CRQ-01 · rév. 1 · 24-09-26 · ESQUISSE · schéma légendé en français

PROJET

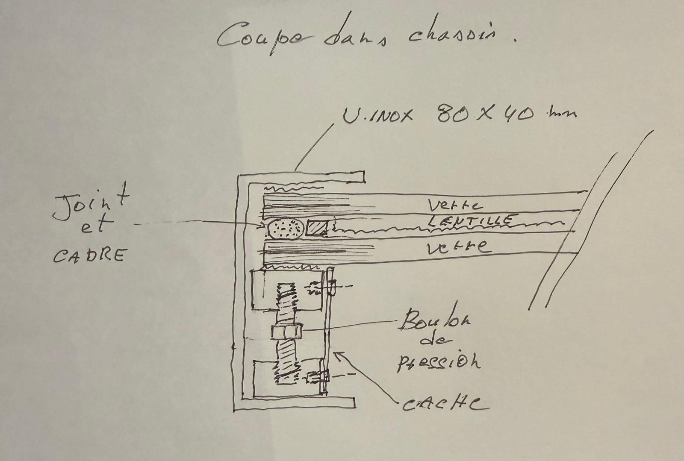
[picture p50: figure]

## LES VEILLEURS — Beaufort 27

ARTISTE · MAÎTRE D'ŒUVRE

## Eva L'Hoest · +32 495 57 92 12 · eva.lhoest@gmail.com

ASSISTANT ÉLECTROMÉCANIQUE

## Gioacchino Miceli · +32 497 84 45 10 · gioacchino.miceli@thefaktory.com

DOCUMENT

## La vitrine lenticulaire — Croquis de principe d'origine — coupe dans le montant

OBJET

## Double vitrage démontable, lenticulaire libre, châssis U inox

N° DOCUMENT · RÉVISION · DATE · HEURE

## LV-VL-CRQ-01 · rév. 1 · 24-09-26

EN LIGNE

### https://vitrine-lenticulaire.vercel.app

STATUT

## ESQUISSE

© Eva L'Hoest 2026 — Confidentiel. Reproduction, diffusion ou usage hors de cette consultation interdits sans accord écrit de l'artiste. Cotes non contractuelles.

1 / 1
