PLHFak/Vitrine_lenticulaire/docs/png/base_mono_bloc_V00.png

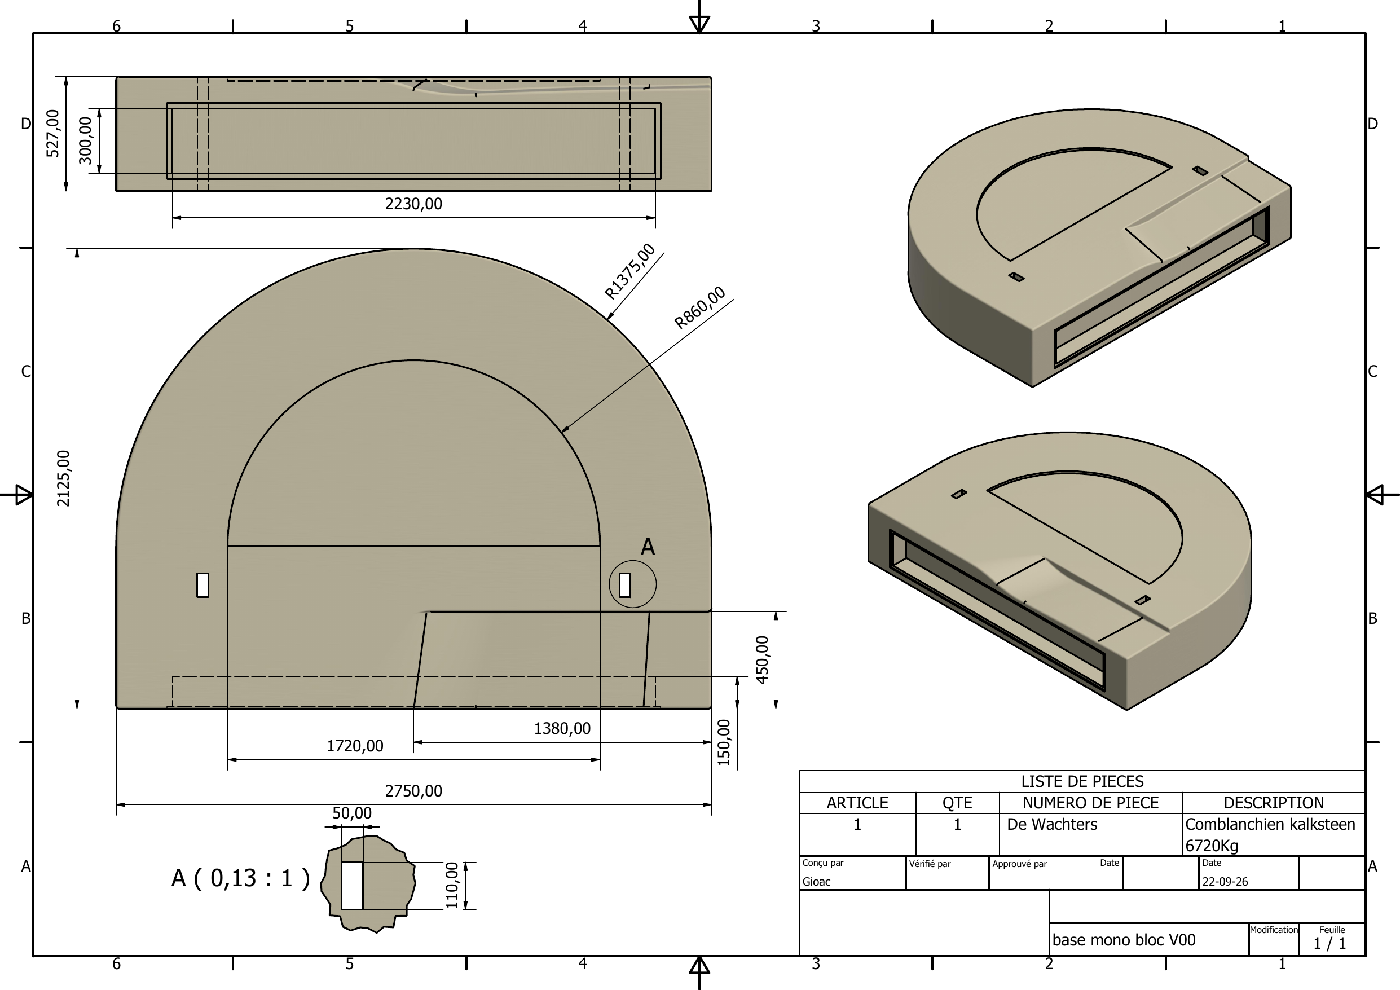
docs/png/base_mono_bloc_V00.png
