PLHFak/Vitrine_lenticulaire/docs/thumbs/fig2_coupe_montant.jpg

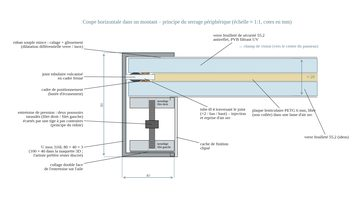
docs/thumbs/fig2_coupe_montant.jpg
