PLHFak/Vitrine_lenticulaire/docs/thumbs/note_v01.jpg

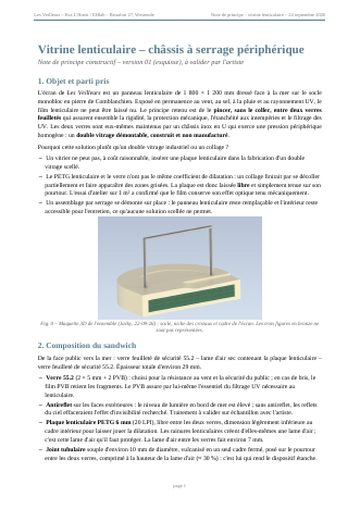
docs/thumbs/note_v01.jpg
