PLHFak/Vitrine_lenticulaire/docs/ao/LV-BA-PL-00_base_mono_bloc_V00_JMiceli.pdf

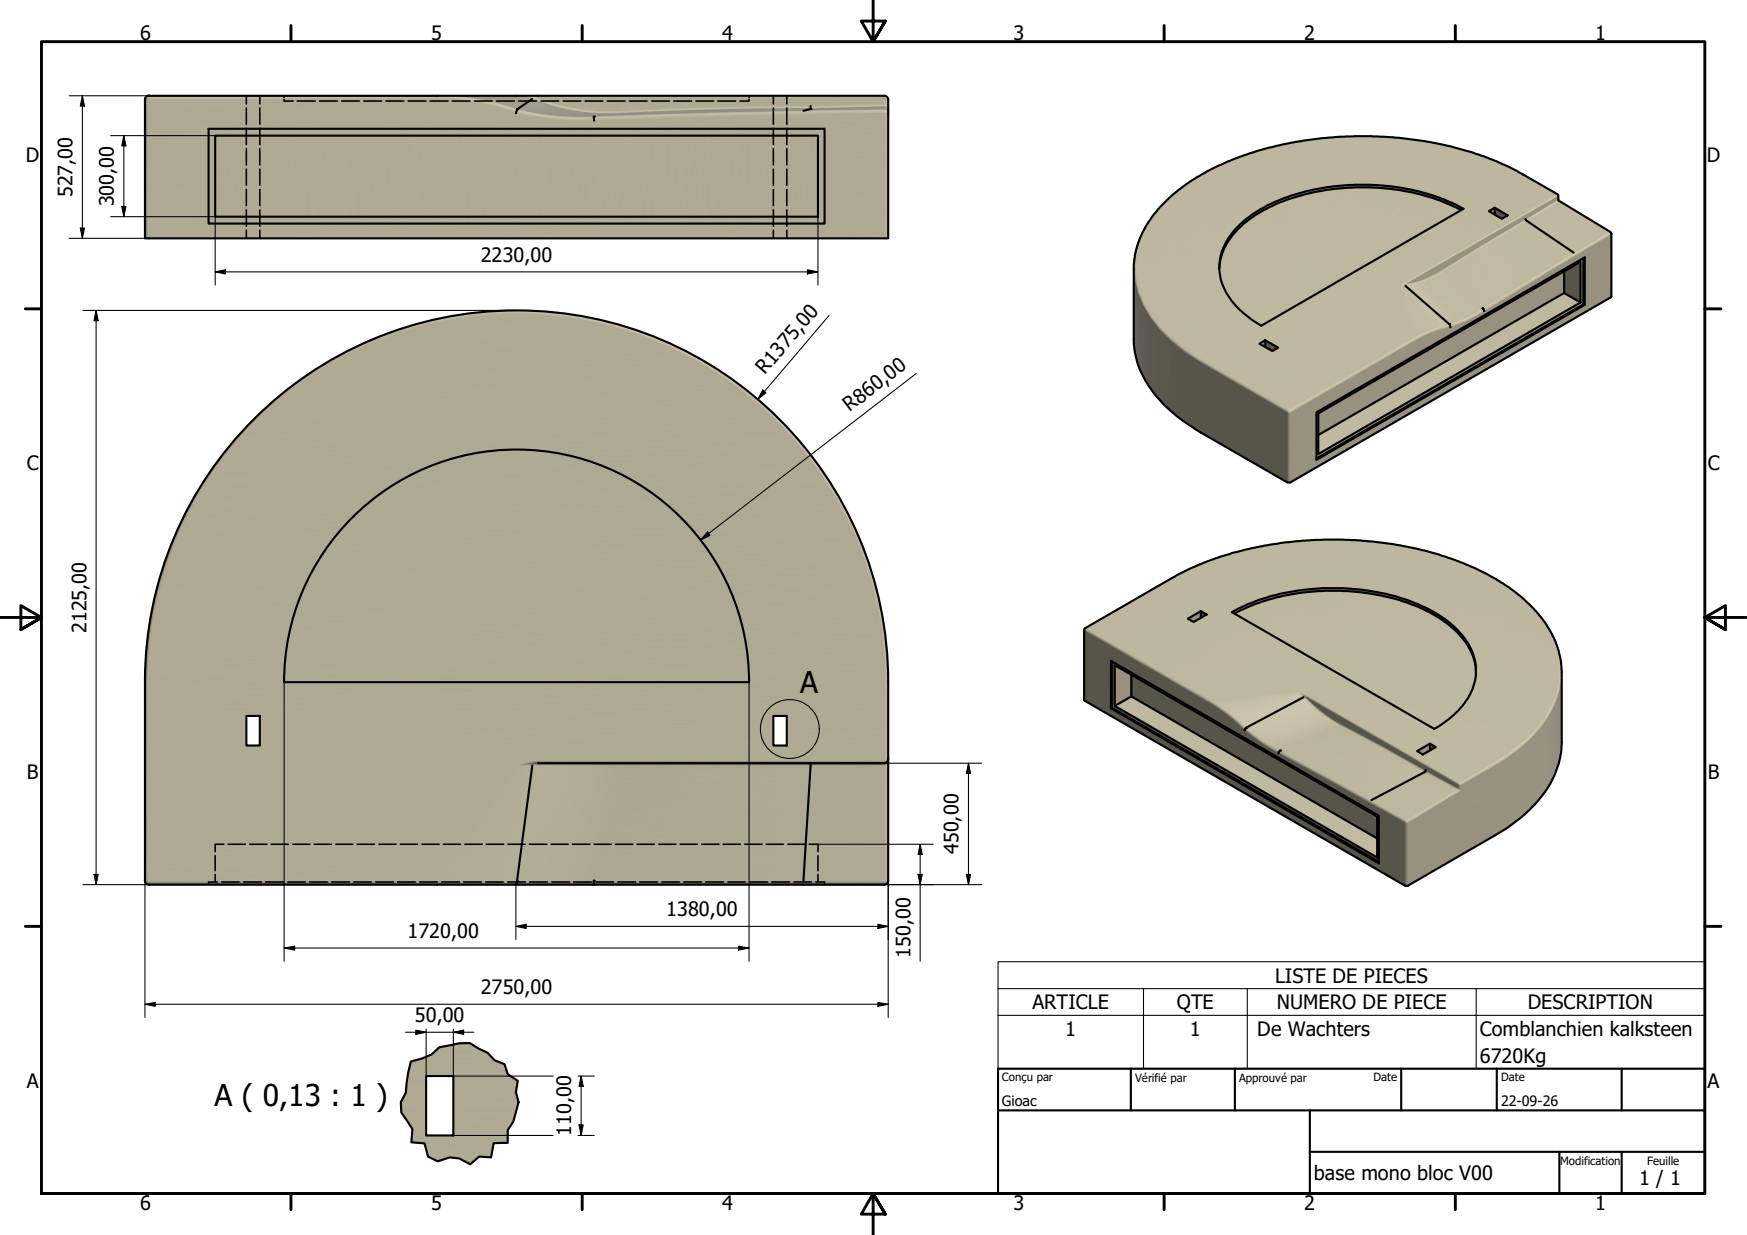
[picture p57: page 1]

LISTE DE PIECES

ARTICLE | QTE | NUMERO DE PIECE | DESCRIPTION
1 | 1 | De Wachters | Comblanchien kalksteen 6720Kg

Conou par Gioac | Vprifip par | Approuvp par Date | | Date 22-09-26

base mono bloc V00
