PLHFak/Vitrine_lenticulaire/docs/ao/LV-BA-PL-02_ensemble_courbe_260922_JMiceli.pdf

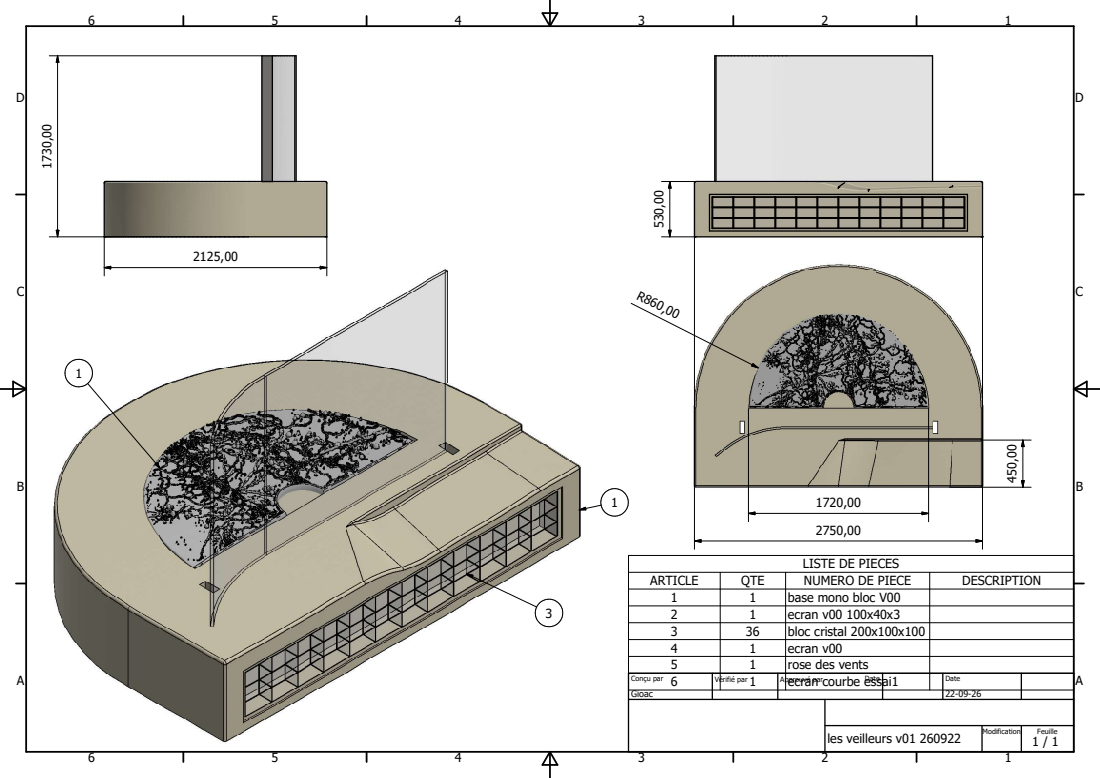
[picture p58: page 1]
les veilleurs v01 260922; Modification; Feuille

LISTE DE PIECES

ARTICLE | QTE | NUMERO DE PIECE | DESCRIPTION
1 | 1 | base mono bloc V00
2 | 1 | ecran v00 100x40x3
3 | 36 | bloc cristal 200x100x100
4 | 1 | ecran v00
5 | 1 | rose des vents

Conçu par 6 | Vérifié par | 1 | Approuvé par | ecran courbe essai1 Date | Date
Gioac | | | | | 22-09-26
